MPlasson/Portable-Voltage-Standard/electronics/simulation/BatteryMonitor.asc

D1: LED; NSCW100
D2: LED; NSCW100
M1: nmos; AO6408
M2: nmos; AO6408
M3: pmos; AO6407
R1: res; 470k
R2: res; 100k
R3: res; 1Meg
R4: res; 300k
R5: res; 300k
R6: res; 100
R7: res; 1k
R8: res; 100
R9: res; 1k
R10: res; 1Meg
R11: res; 100
U1: UniversalOpAmp2
V1: voltage; 2.5
V2: voltage; PULSE(9 5 0 1 1 1)
Named nets: 0, vcc, vbatt, scaled_vbatt
.tran 3
http://sim.okawa-denshi.jp/en/compkeisan.htm
