MPlasson/Portable-Voltage-Standard/electronics/simulation/DCAmplifier.asc

Q1: npn; 2N3904
Q2: pnp; 2N3906
Q3: pnp; 2N3906
R1: res; 10k
R2: res; 10k
R3: res; 390
R4: res; 10k
R5: res; 470k
V1: voltage; -30
V2: voltage; +30
V3: voltage; PULSE(-15 15 0 1 1 1 1)
V4: voltage; -15
Named nets: VEE, VCC, gain_out, VEE_15, 0, input
.tran 1
Set the TF such as input=0 coincide with output=0
