MPlasson/Portable-Voltage-Standard/electronics/simulation/PVS_v1.asc

C1: cap; 22n
C2: cap; 10n
C3: cap; 100p
C4: cap; 10n
C5: cap; 1n
C6: cap; 10n
D1: diode; 1N4148
D2: diode; 1N4148
D3: diode; 1N4148
D4: zener; BZX84C15L
D5: zener; BZX84C15L
D6: diode; 1N4148
D7: diode; 1N4148
D8: diode; 1N4148
D9: schottky; 1N5817
Q1: npn; 2SCR583D3
Q2: pnp; 2SAR583D3
Q3: npn; 2N3904
Q4: pnp; 2N3906
Q5: npn; 2N3904
Q6: pnp; 2N3906
Q7: pnp; 2N3906
Q8: npn; 2N3904
Q9: pnp; 2N3906
Q10: npn; 2N3904
Q11: pnp; 2N3906
Q12: pnp; 2N3906
Q13: npn; 2N3904
Q14: pnp; 2N3906
Q15: npn; 2N3904
Q16: pnp; 2N3906
Q17: pnp; 2N3906
Q18: pnp; 2N3906
Q19: npn; 2N3904
Q20: pnp; 2N3906
Q21: npn; 2N3904
Q24: npn; 2N3904
R1: res; 10k
R2: res; 10k
R3: res; 9k
R4: res; 1k
R5: res; 5
R6: res; 1k
R7: res; 5
R8: res; 250
R9: res; 500k
R10: res; 10k
R11: res; 470
R12: res; 500k
R13: res; 10k
R14: res; 1k
R15: res; 10k
R16: res; 47k
R17: res; 10k
R18: res; 1k
R19: res; 47k
R20: res; 10k
R21: res; 10k
R22: res; 10k
R23: res; 10k
R24: res; 1k
R25: res; 1k
R26: res; 10k
R27: res; 10k
R28: res; 10k
R29: res; 390
R30: res; 10k
R31: res; 470k
R32: res; 47k
R33: res; 10k
R34: res; 10k
R35: res; 47k
R36: res; 10k
R37: res; 10k
R38: res; 1k
R39: res; 10k
R41: res; 10k
R42: res; 47k
R44: res; 10k
U1: OPAx196
U2: OPAx196
U3: OPAx196
V1: voltage; -30
V2: voltage; +30
V3: voltage; -15
V4: voltage; +15
Vdac: voltage; PULSE(-2.5 2.5 20m 1u 1u 100m 1)
Named nets: 0, VCC, VEE, VCC_15, VEE_15, main_output, OC, int_out, gain_out, servo, nSTAB, STAB
.tran 200m startup uic
Overcurrent detection circuit
High power buffer
Bootstrapped opamp
Slope control
DC servo
DC amplifier
Stability detection circuit (inverted)
Stability detection circuit (non-inverted)
